gaveshalabs/weatherkids-hardware/Version 2.0/Core/Prelim Desing/Procuments details/HS Code confimation letter..pdf

Deputy Director of Customs

Customs Department Katunayake,

Sri Lanka

Dear Deputy Director,

I hope this letter finds you well. I am writing to approve the clearance process of my educational weather computer device under HS Code 9025.90, as you concluded after the inspection.

Thank you for your cooperation.

Sincerely,

Ushan Chaminda

Educator/ Engineer
