gaveshalabs/weatherkids-hardware/Version 2.0/Core/Prelim Desing/Procuments details/Invoice.pdf

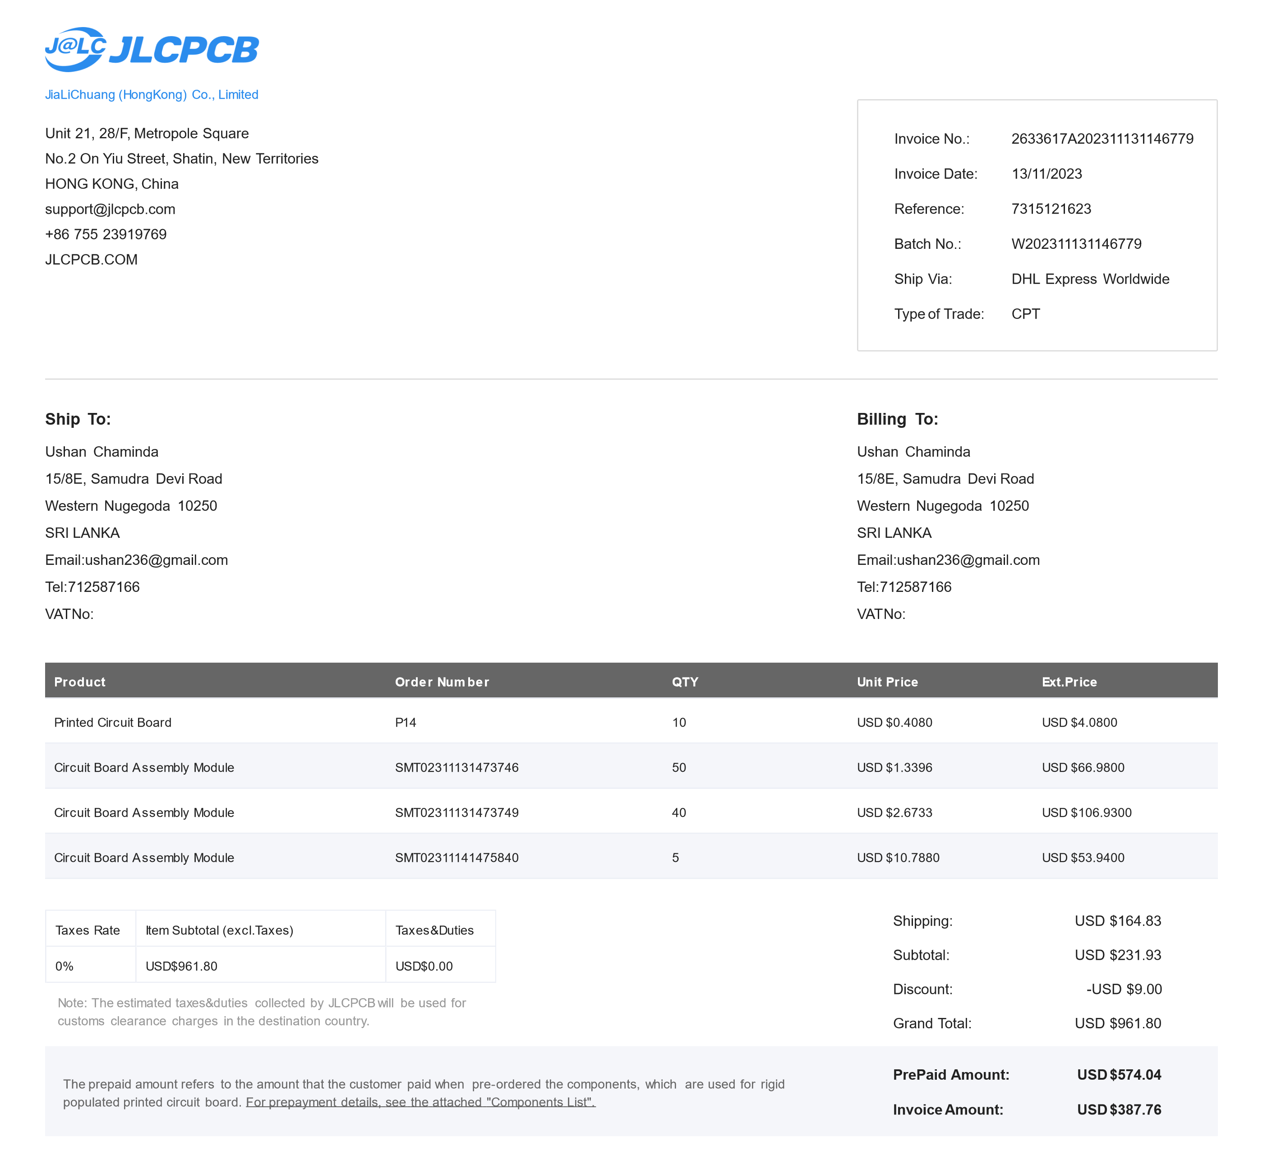
[picture p2: page 1]
