gaveshalabs/weatherkids-hardware/Version 2.0/Core/Weather Computer/_CAD Files/Stickers/Rain Scale - Laminated.pdf

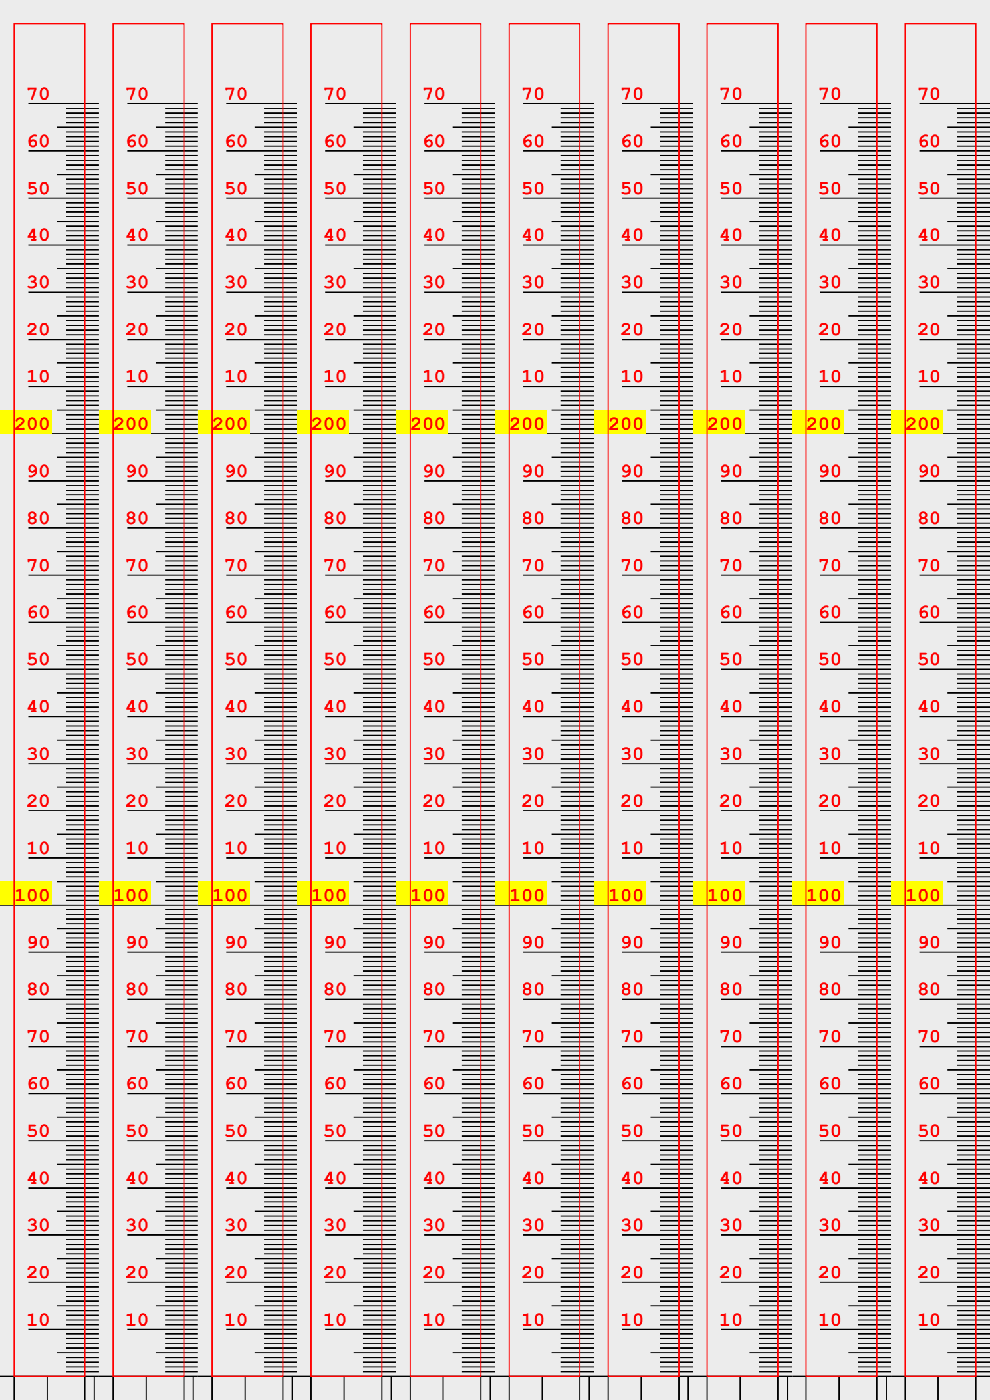
[picture p3: figure]
