gaveshalabs/weatherkids-hardware/Version 2.0/Core/Weather Computer/Resources/Connectors/DC-044D-2.5A-2.5-SMT.pdf

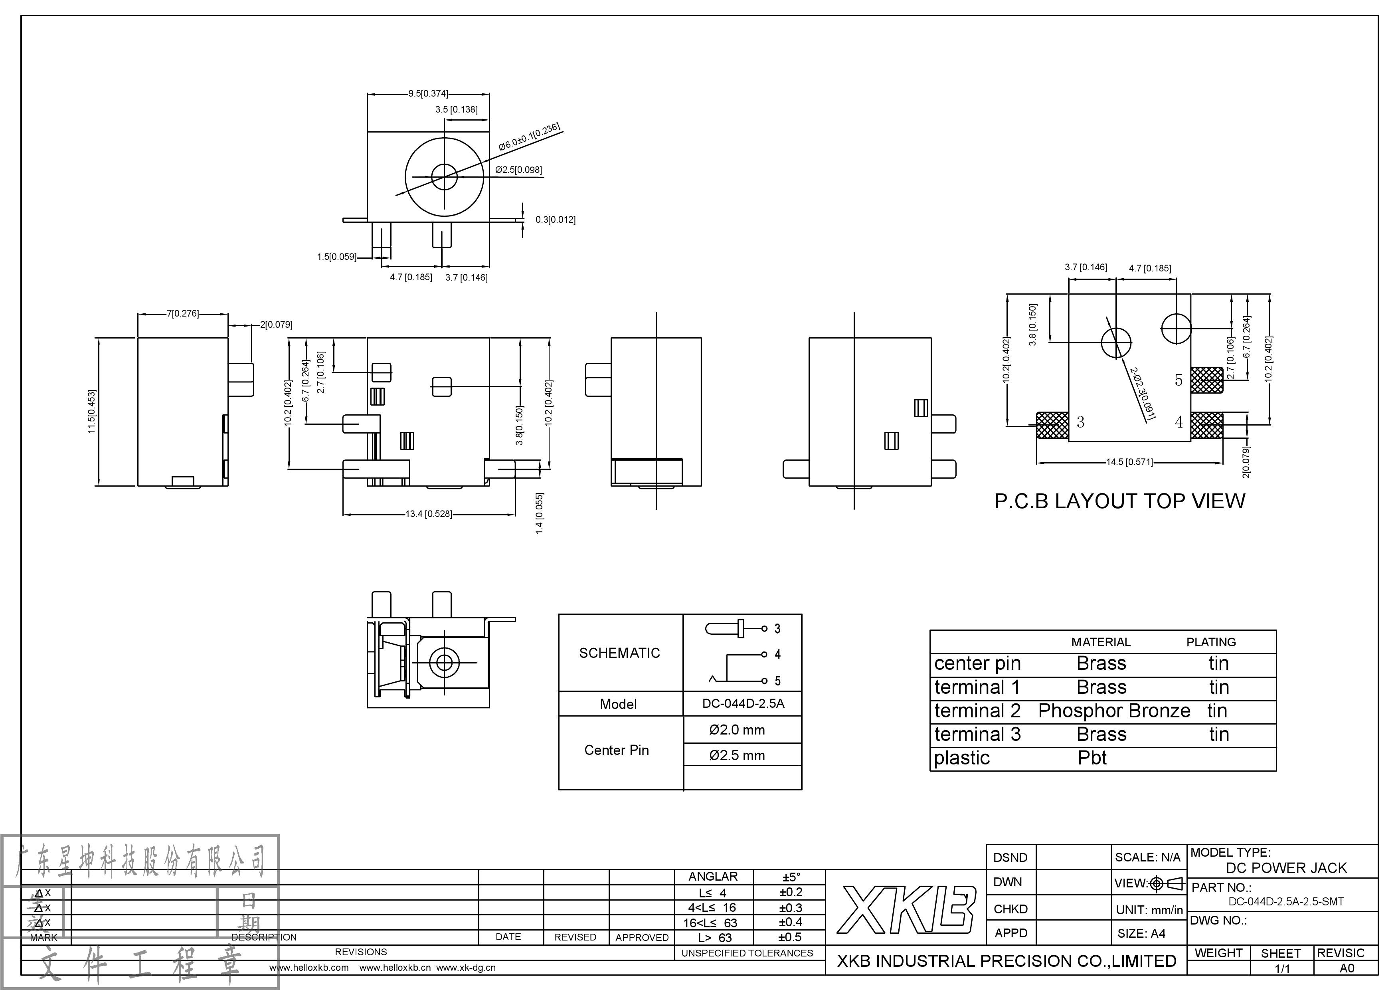
[picture p4: page 1]
