gaveshalabs/weatherkids-hardware/Version 2.0/Core/Weather Computer/Notes/Connectors.xlsx

part | price | link
RJ11 port | 0.16 | https://jlcpcb.com/partdetail/203237-R_RJ11R06PA800/C189750
