gaveshalabs/weatherkids-hardware/Version 2.0/Core/Weather Computer/Resources/3D Models/S2B-PH-SM4-TB(LF)(SN)--3DModel-STEP-56544.STEP

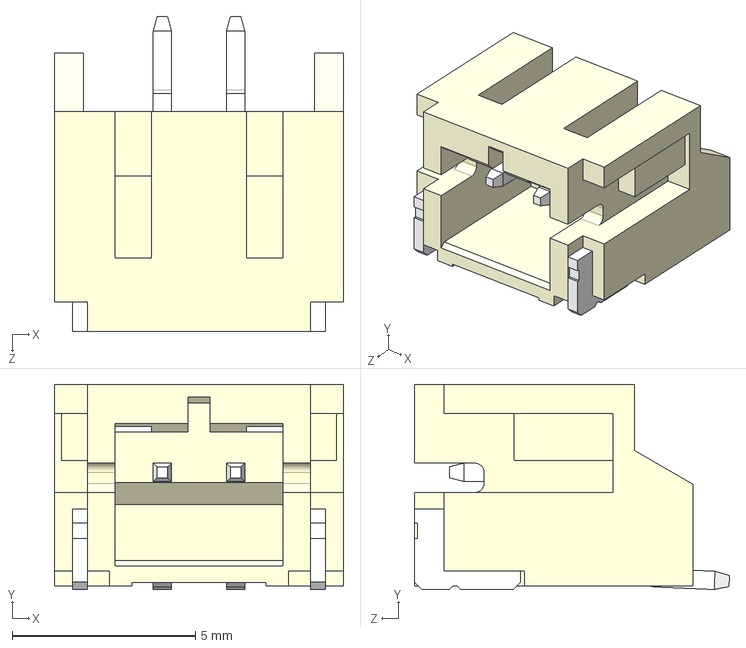
[picture p14: CAD file, 2024-11-12]
Version 2.0/Core/Weather Computer/Resources/3D Models/S2B-PH-SM4-TB(LF)(SN)--3DModel-STEP-56544.STEP
7.90 x 5.60 x 8.60 mm
