gaveshalabs/weatherkids-hardware/Version 2.0/Core/Weather Computer/Resources/USB C/usb-connector-type-c-female-1.snapshot.1/usb-type-c-smd-12pin-smd-1.snapshot.1/USB_type_C_smd_12ps.stp

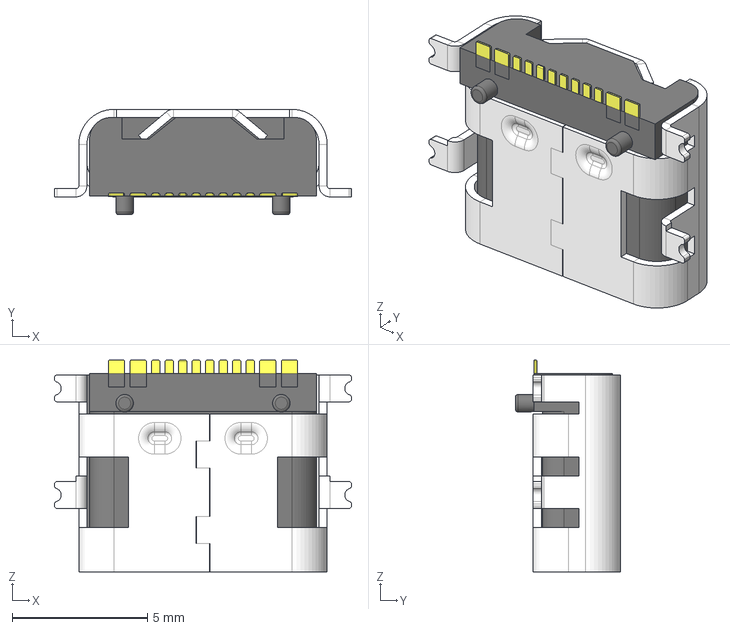
[picture p15: CAD file, 2024-11-12]
Version 2.0/Core/Weather Computer/Resources/USB C/usb-connector-type-c-female-1.snapshot.1/usb-type-c-smd-12pin-smd-1.snapshot.1/USB_type_C_smd_12ps.stp
11.0 x 3.90 x 7.85 mm
