gaveshalabs/weatherkids-hardware/Version 2.0/Solar Action Card/ENC/Production/SA_Bottom.STL

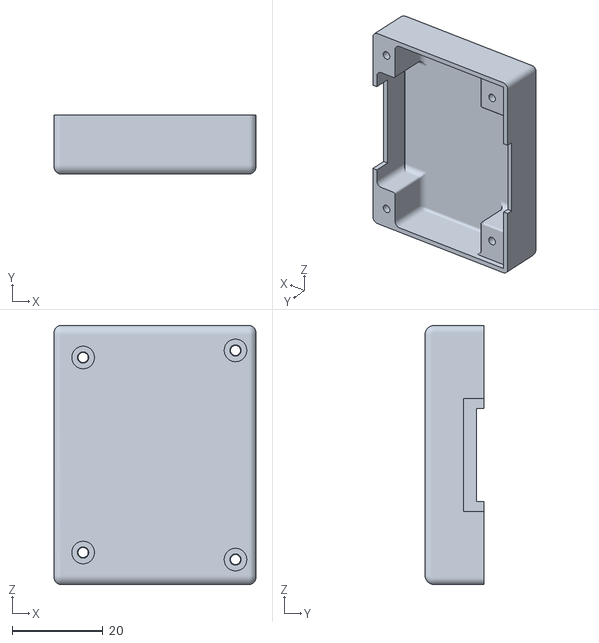
[picture p16: CAD file, 2024-11-12]
Version 2.0/Solar Action Card/ENC/Production/SA_Bottom.STL
44.5 x 13.0 x 57.1
