gaveshalabs/weatherkids-hardware/Version 2.0/Core/Weather Computer/_CAD Files/3D designs/OUTPUT/Clip mount.stl

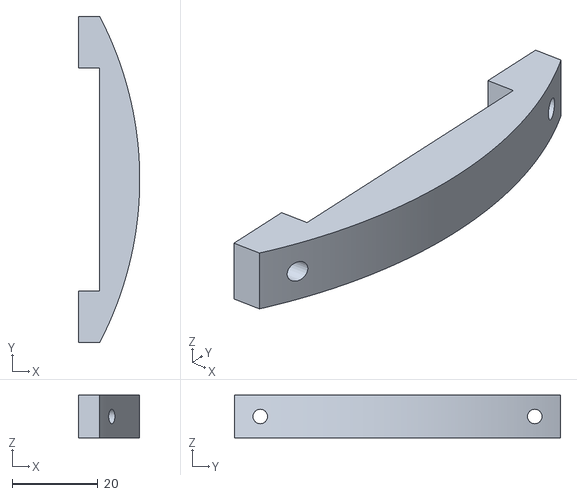
[picture p17: CAD file, 2024-11-12]
Version 2.0/Core/Weather Computer/_CAD Files/3D designs/OUTPUT/Clip mount.stl
14.3 x 76.0 x 10.00
