gaveshalabs/weatherkids-hardware/Version 2.0/Core/Weather Computer/_CAD Files/Parts/db125-35-8p-s.stp

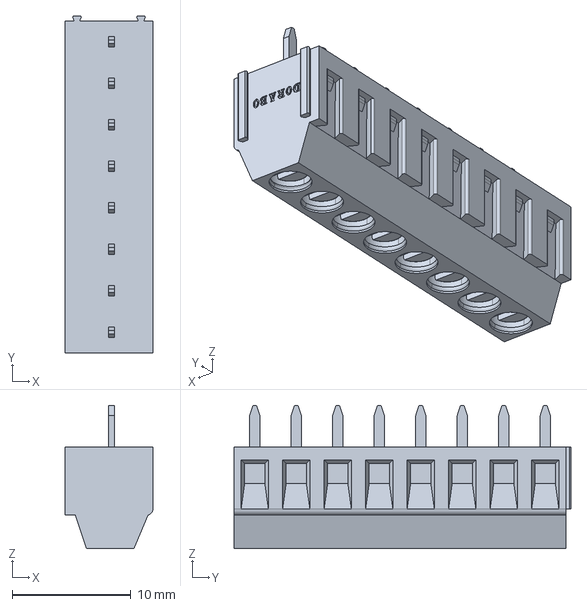
[picture p18: CAD file, 2024-11-12]
Version 2.0/Core/Weather Computer/_CAD Files/Parts/db125-35-8p-s.stp
7.40 x 28.4 x 12.1 mm
