gaveshalabs/weatherkids-hardware/Version 2.0/Solar Action Card/ENC/Production/SA_Top.STL

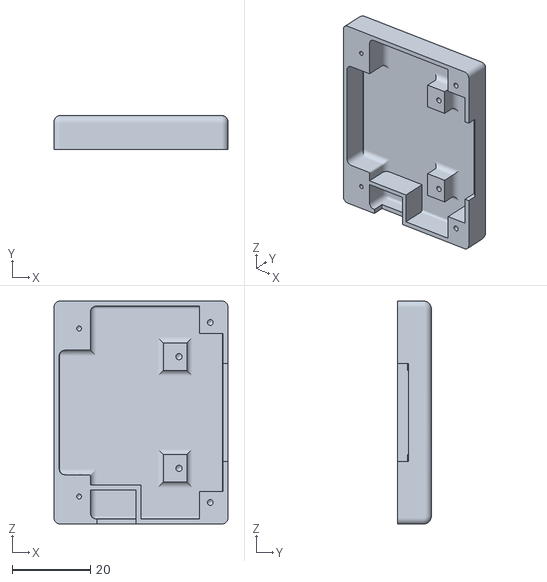
[picture p19: CAD file, 2024-11-12]
Version 2.0/Solar Action Card/ENC/Production/SA_Top.STL
44.5 x 8.65 x 57.1
