gaveshalabs/weatherkids-hardware/Version 2.0/Core/Weather Computer/_CAD Files/3D designs/OUTPUT/WS Pole Clip.stl

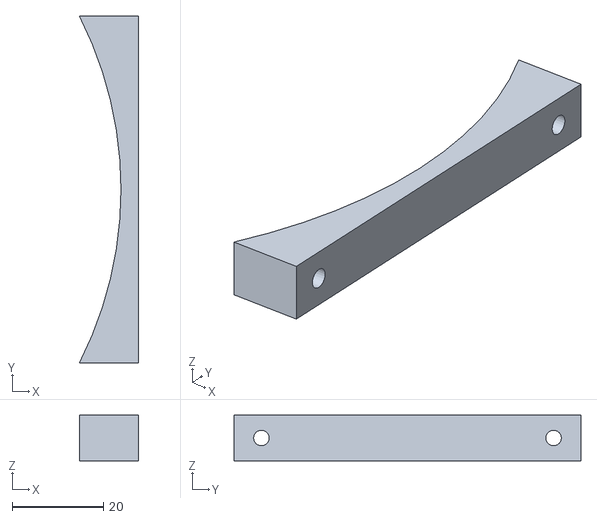
[picture p20: CAD file, 2024-11-12]
Version 2.0/Core/Weather Computer/_CAD Files/3D designs/OUTPUT/WS Pole Clip.stl
13.0 x 76.0 x 10.0
