gaveshalabs/weatherkids-hardware/Version 2.0/Core/Weather Computer/_CAD Files/Parts/db125-381-2p-s.stp

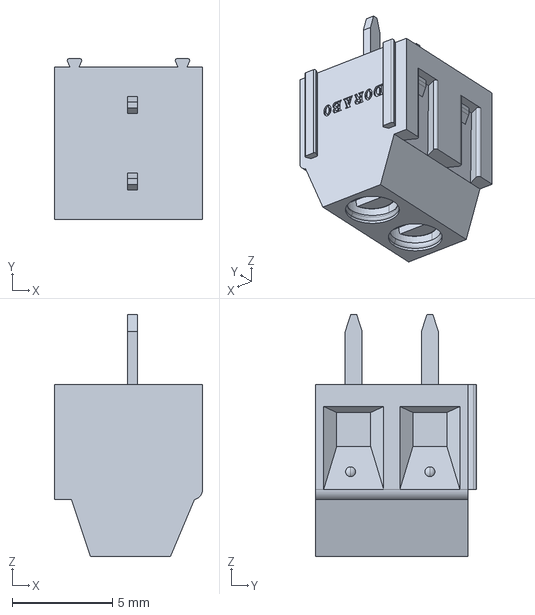
[picture p21: CAD file, 2024-11-12]
Version 2.0/Core/Weather Computer/_CAD Files/Parts/db125-381-2p-s.stp
7.40 x 8.04 x 12.1 mm
