gaveshalabs/weatherkids-hardware/Version 2.0/Core/Weather Computer/ENC/Production/WC_Button.STL

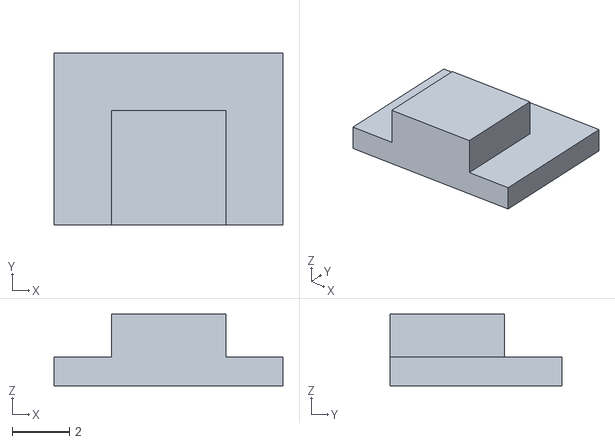
[picture p22: CAD file, 2024-11-12]
Version 2.0/Core/Weather Computer/ENC/Production/WC_Button.STL
8.00 x 6.00 x 2.50
