gaveshalabs/weatherkids-hardware/Version 2.0/Core/Weather Computer/ENC/WC_Button_Left.SLDPRT

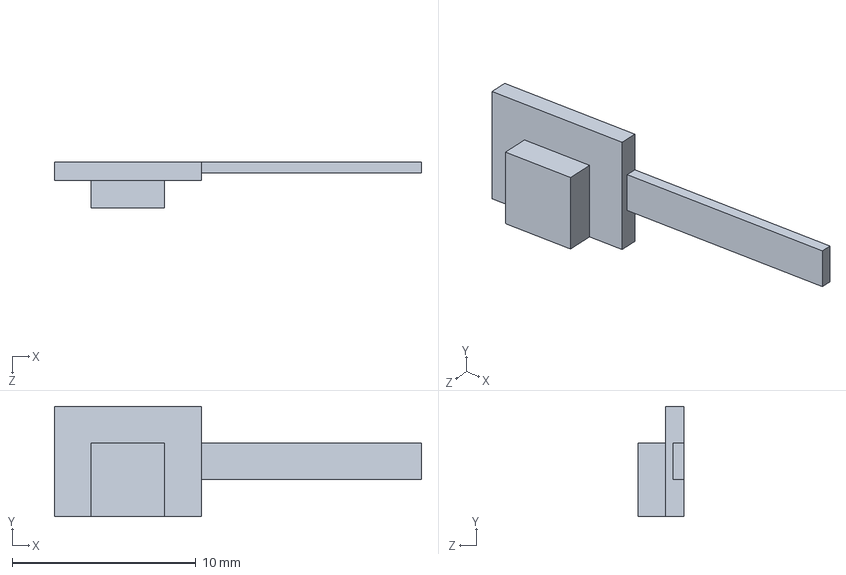
[picture p23: CAD file, 2024-11-12]
Version 2.0/Core/Weather Computer/ENC/WC_Button_Left.SLDPRT
20.0 x 6.00 x 2.50 mm
