gaveshalabs/weatherkids-hardware/Version 2.0/Core/Weather Computer/_CAD Files/3D designs/OUTPUT/Bucket Bracket.stl

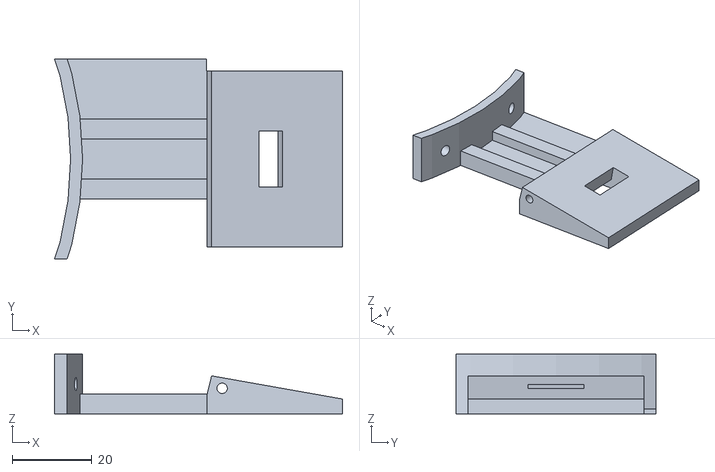
[picture p24: CAD file, 2024-11-12]
Version 2.0/Core/Weather Computer/_CAD Files/3D designs/OUTPUT/Bucket Bracket.stl
72.0 x 50.0 x 15.0
