gaveshalabs/weatherkids-hardware/Version 2.0/Core/Weather Computer/_CAD Files/3D designs/OUTPUT/WK Top.stl

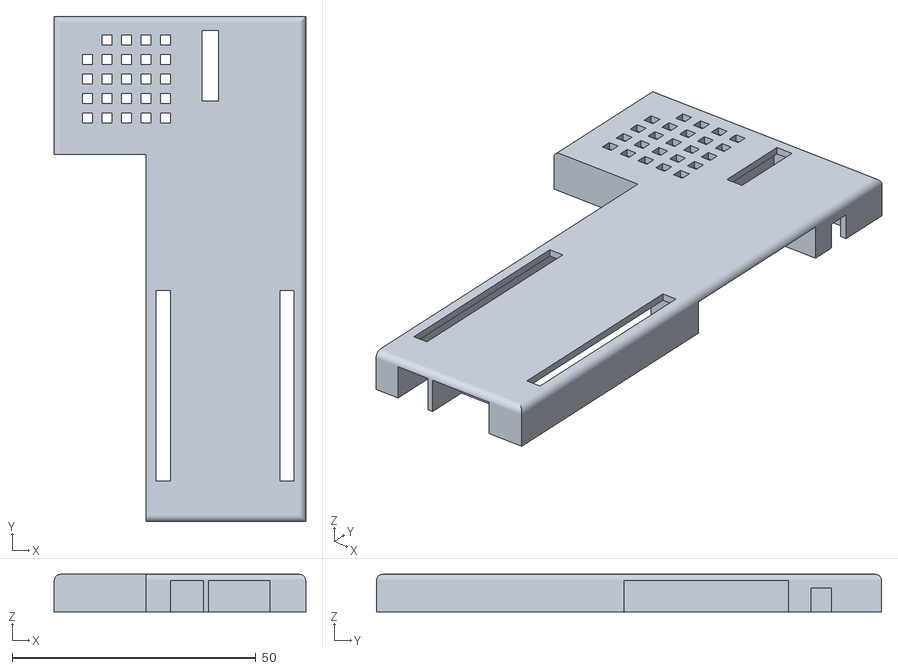
[picture p25: CAD file, 2024-11-12]
Version 2.0/Core/Weather Computer/_CAD Files/3D designs/OUTPUT/WK Top.stl
51.6 x 103.6 x 7.70
