gaveshalabs/weatherkids-hardware/Version 2.0/Core/Weather Computer/_CAD Files/3D designs/OUTPUT/WK Bottom.stl

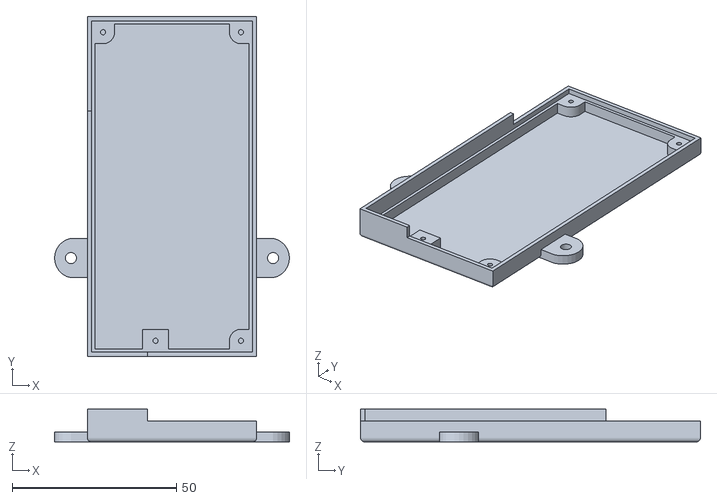
[picture p26: CAD file, 2024-11-12]
Version 2.0/Core/Weather Computer/_CAD Files/3D designs/OUTPUT/WK Bottom.stl
71.6 x 103.6 x 10.0
