gaveshalabs/weatherkids-hardware/Version 2.0/Core/Weather Computer/_CAD Files/3D designs/OUTPUT/WS mini Solar mounter.stl

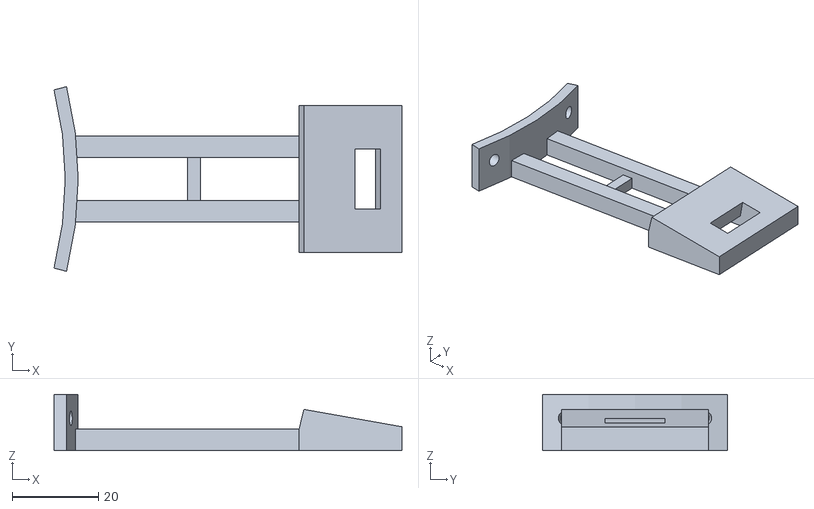
[picture p27: CAD file, 2024-11-12]
Version 2.0/Core/Weather Computer/_CAD Files/3D designs/OUTPUT/WS mini Solar mounter.stl
80.6 x 42.8 x 13.0
