gaveshalabs/weatherkids-hardware/Version 2.0/Core/Weather Computer/Resources/Connectors/MYOUNG-BH-18650-B1BA002_C2988620.pdf

环保

RoHs | K型

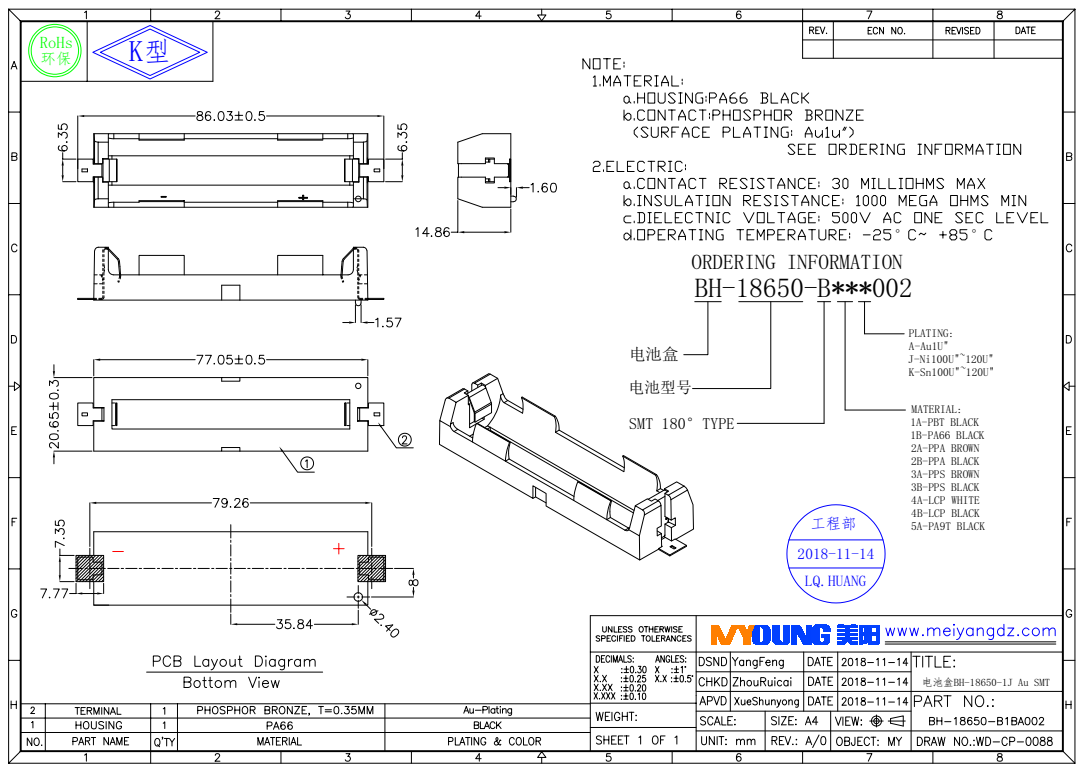
[picture p33: page 1]
工程部; LQ.HUANG; ORDERING INFORMATION; PLATING: A-Au1U" J-Ni100U"~120U" K-Sn100U"~120U"; SMT 180°TYPE; MATERIAL: 1A-PBT BLACK 1B-PA66 BLACK 2A-PPA BROWN 2B-PPA BLACK 3A-PPS BROWN 3B-PPS BLACK 4A-LCP WHITE 4B-LCP BLACK 5A-PA9T BLACK; 电池盒; 电池型号

电池盒BH-18650-1J Au SMT
