gaveshalabs/weatherkids-hardware/Version 2.0/Core/Weather Computer/Notes/R-RJ11R06P-A800.pdf

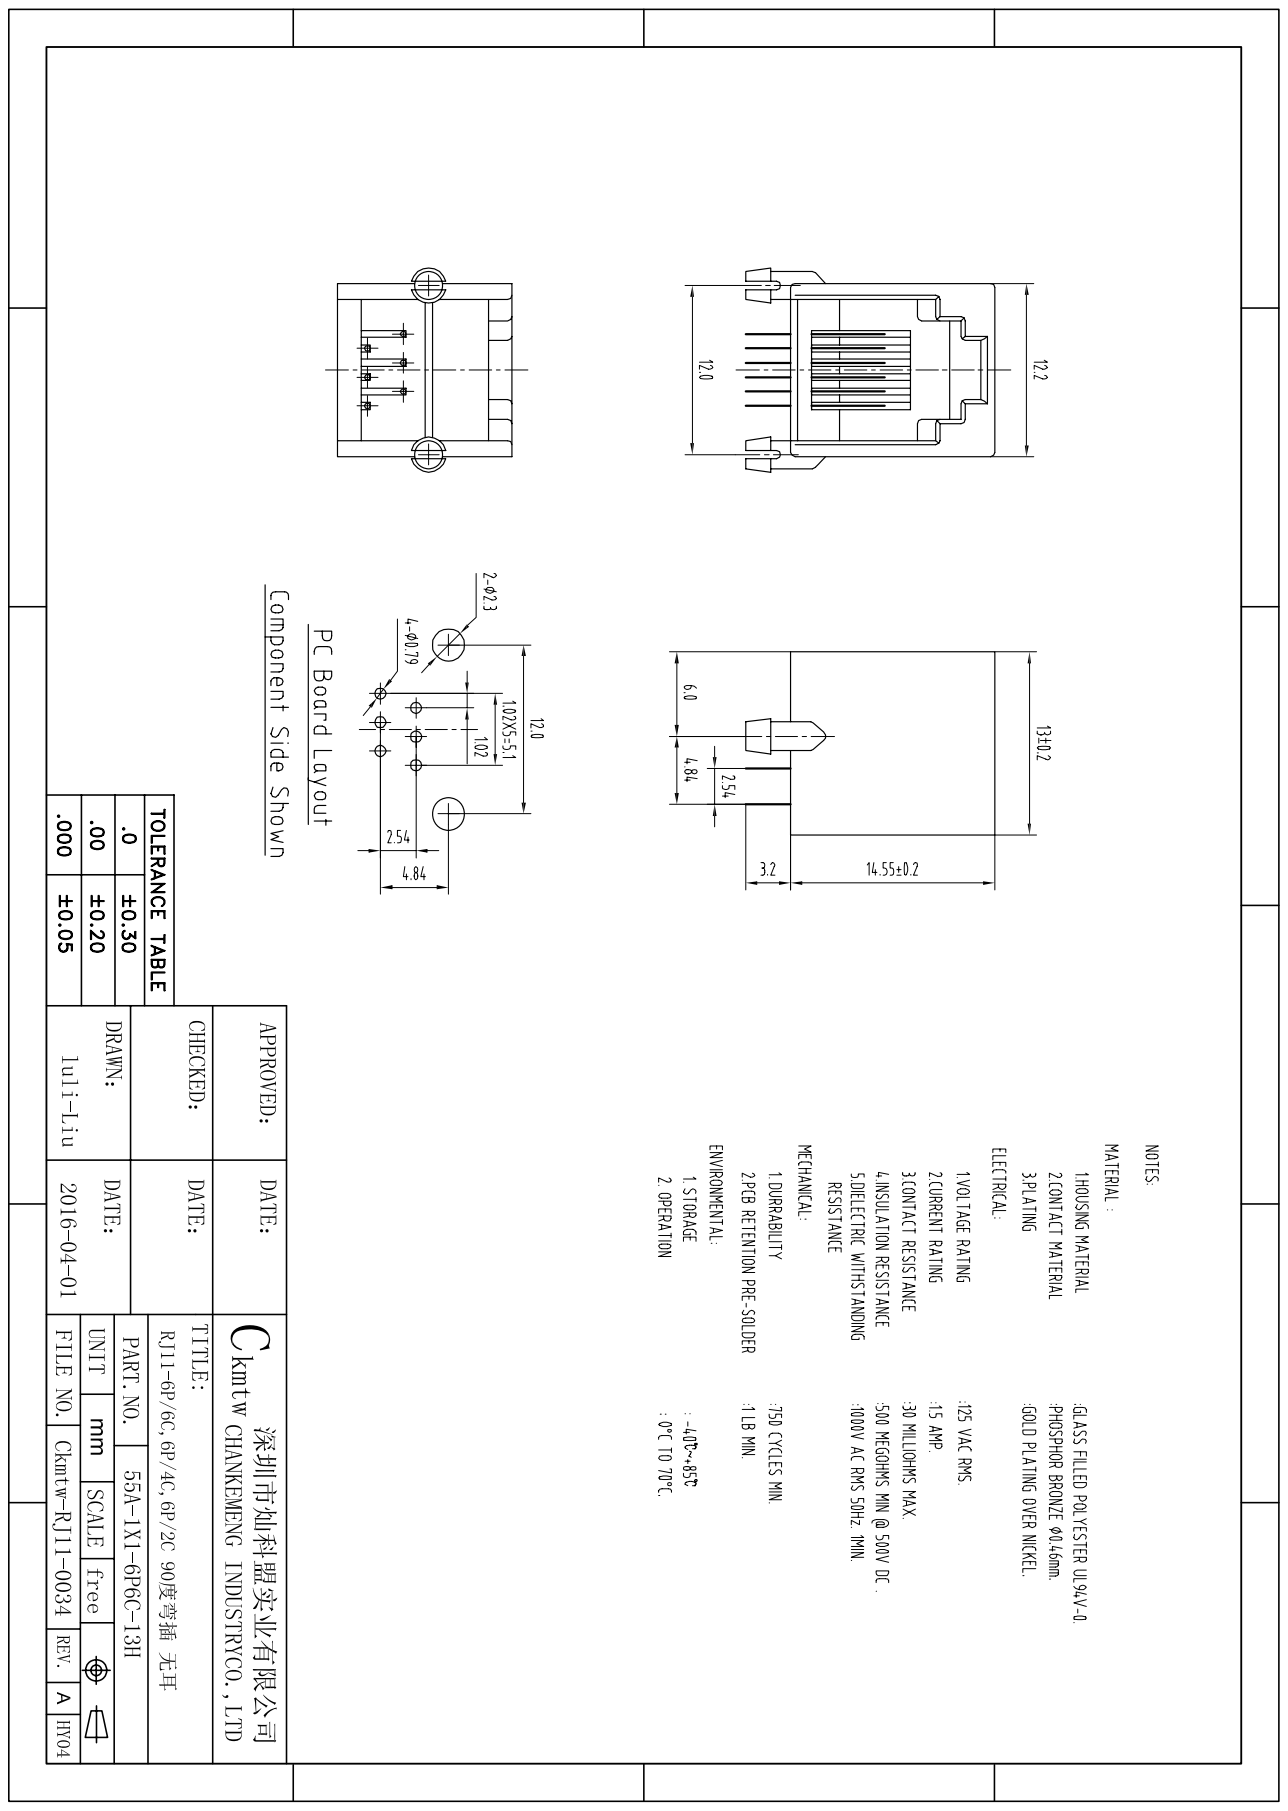
[picture p40: page 1]
