gaveshalabs/weatherkids-hardware/Version 2.0/Core/Weather Computer/_CAD Files/Stickers/Input Box Sticker.pdf

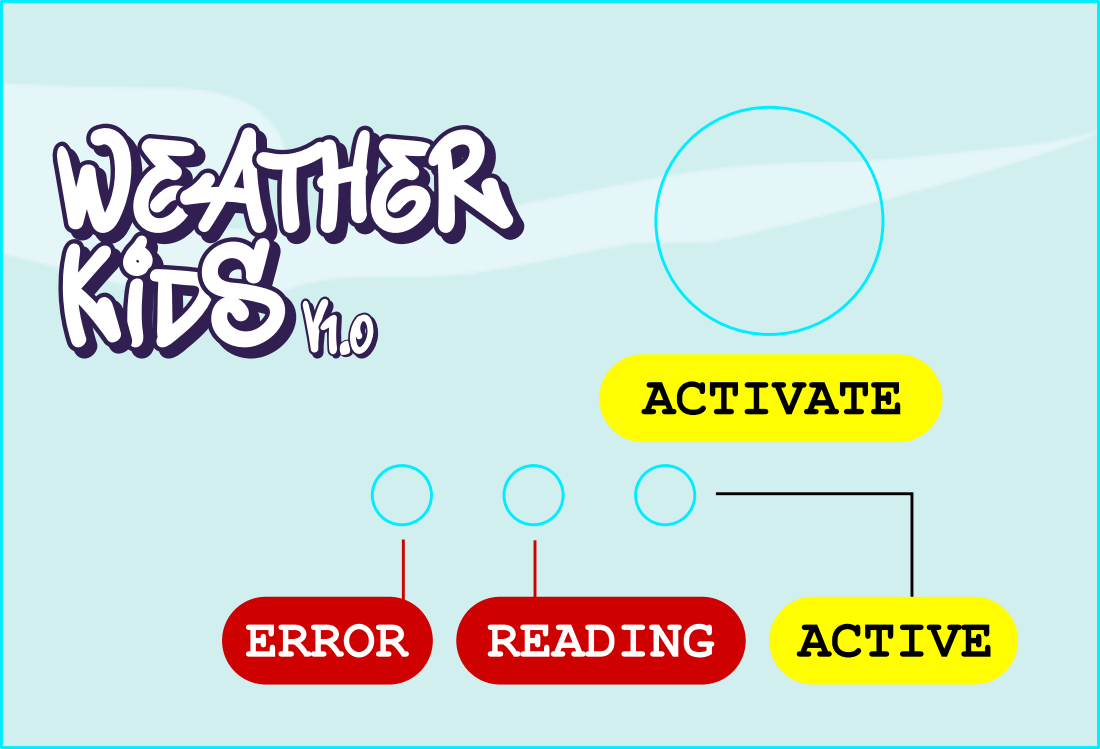
[picture p41: page 1]
READING; ACTIVATE; ERROR; ACTIVE
