gaveshalabs/weatherkids-hardware/Version 1.0/WeatherKids_Compact(V1.0)/_CAD Files/Stickers/SKU Sticker -  Laminated.pdf

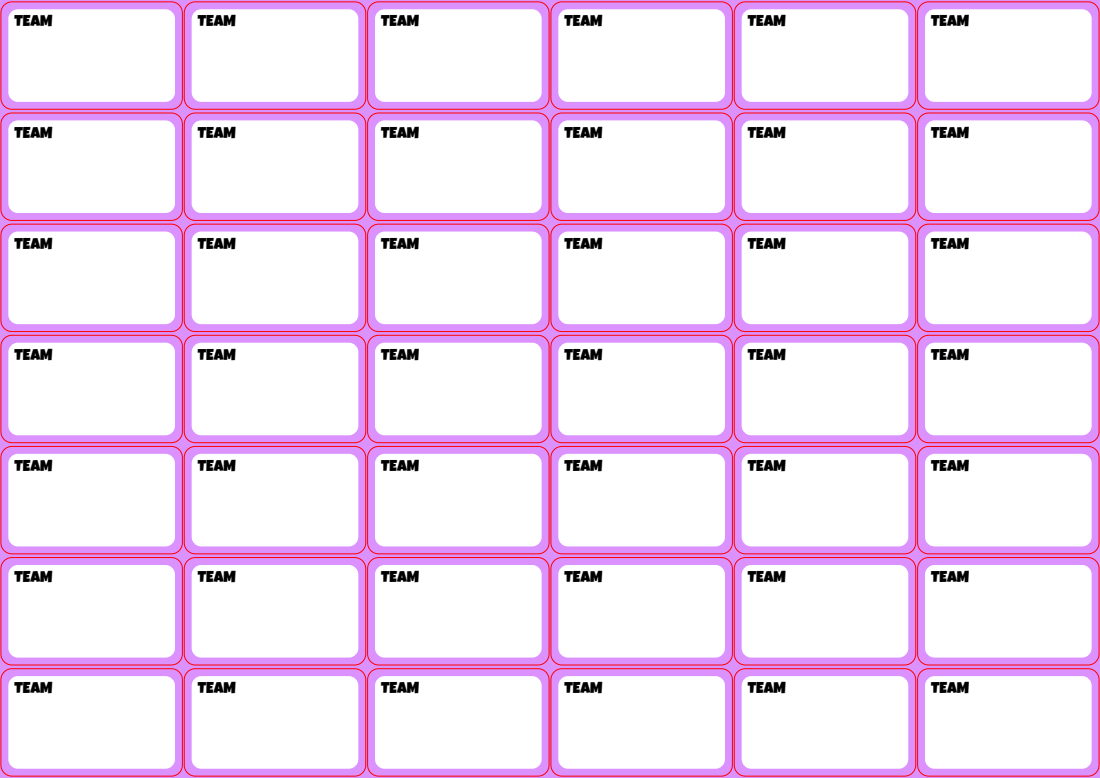
[picture p42: page 1]

TEAM | TEAM | TEAM | TEAM | TEAM | TEAM
