gaveshalabs/weatherkids-hardware/Version 2.0/Core/Weather Computer/_CAD Files/Stickers/Weather Station Notice board.pdf

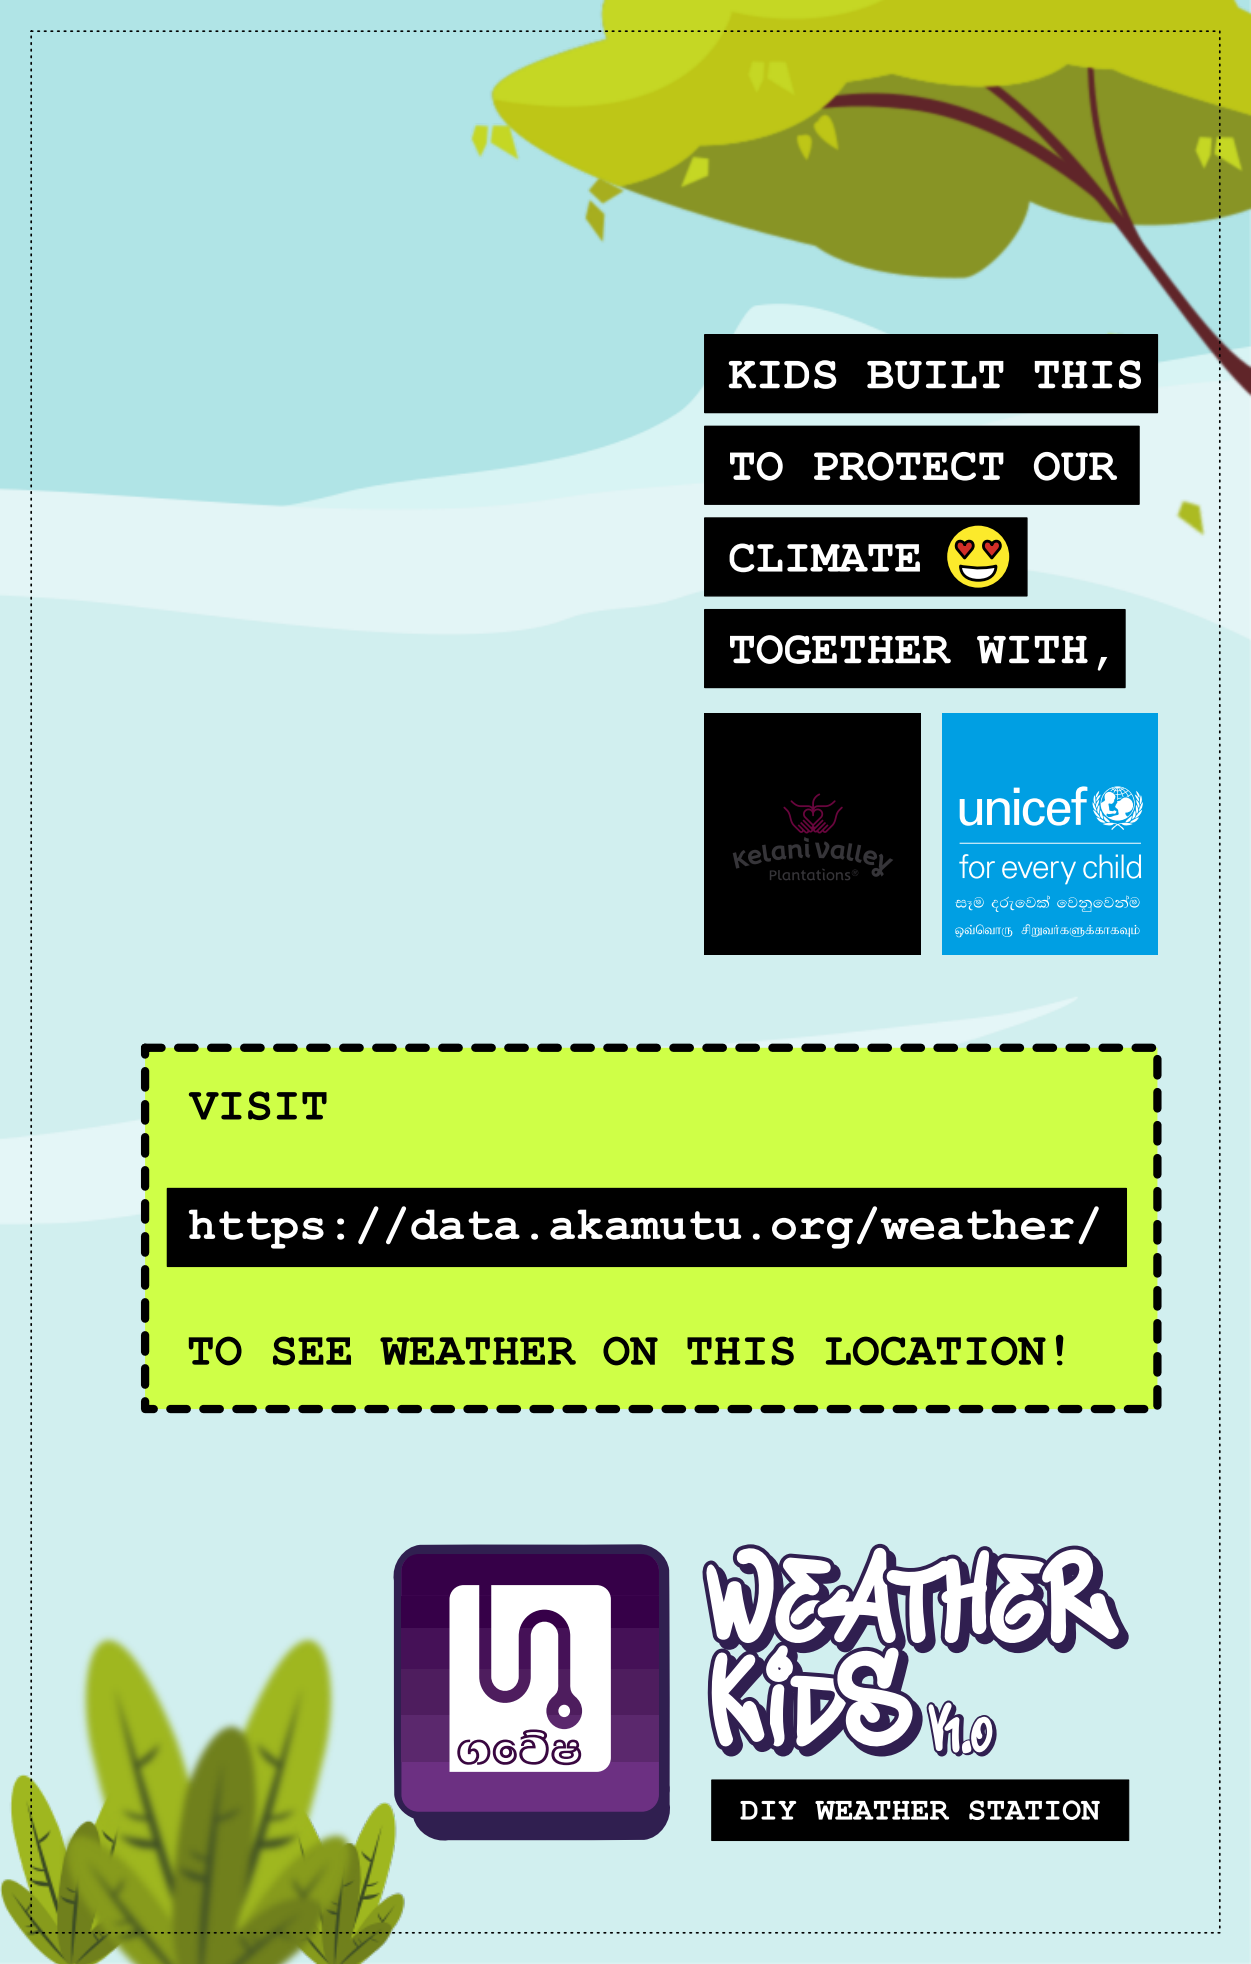
[picture p43: page 1]
