gaveshalabs/weatherkids-hardware/Version 2.0/Core/Weather Computer/Resources/Connectors/MY-18650-02.pdf

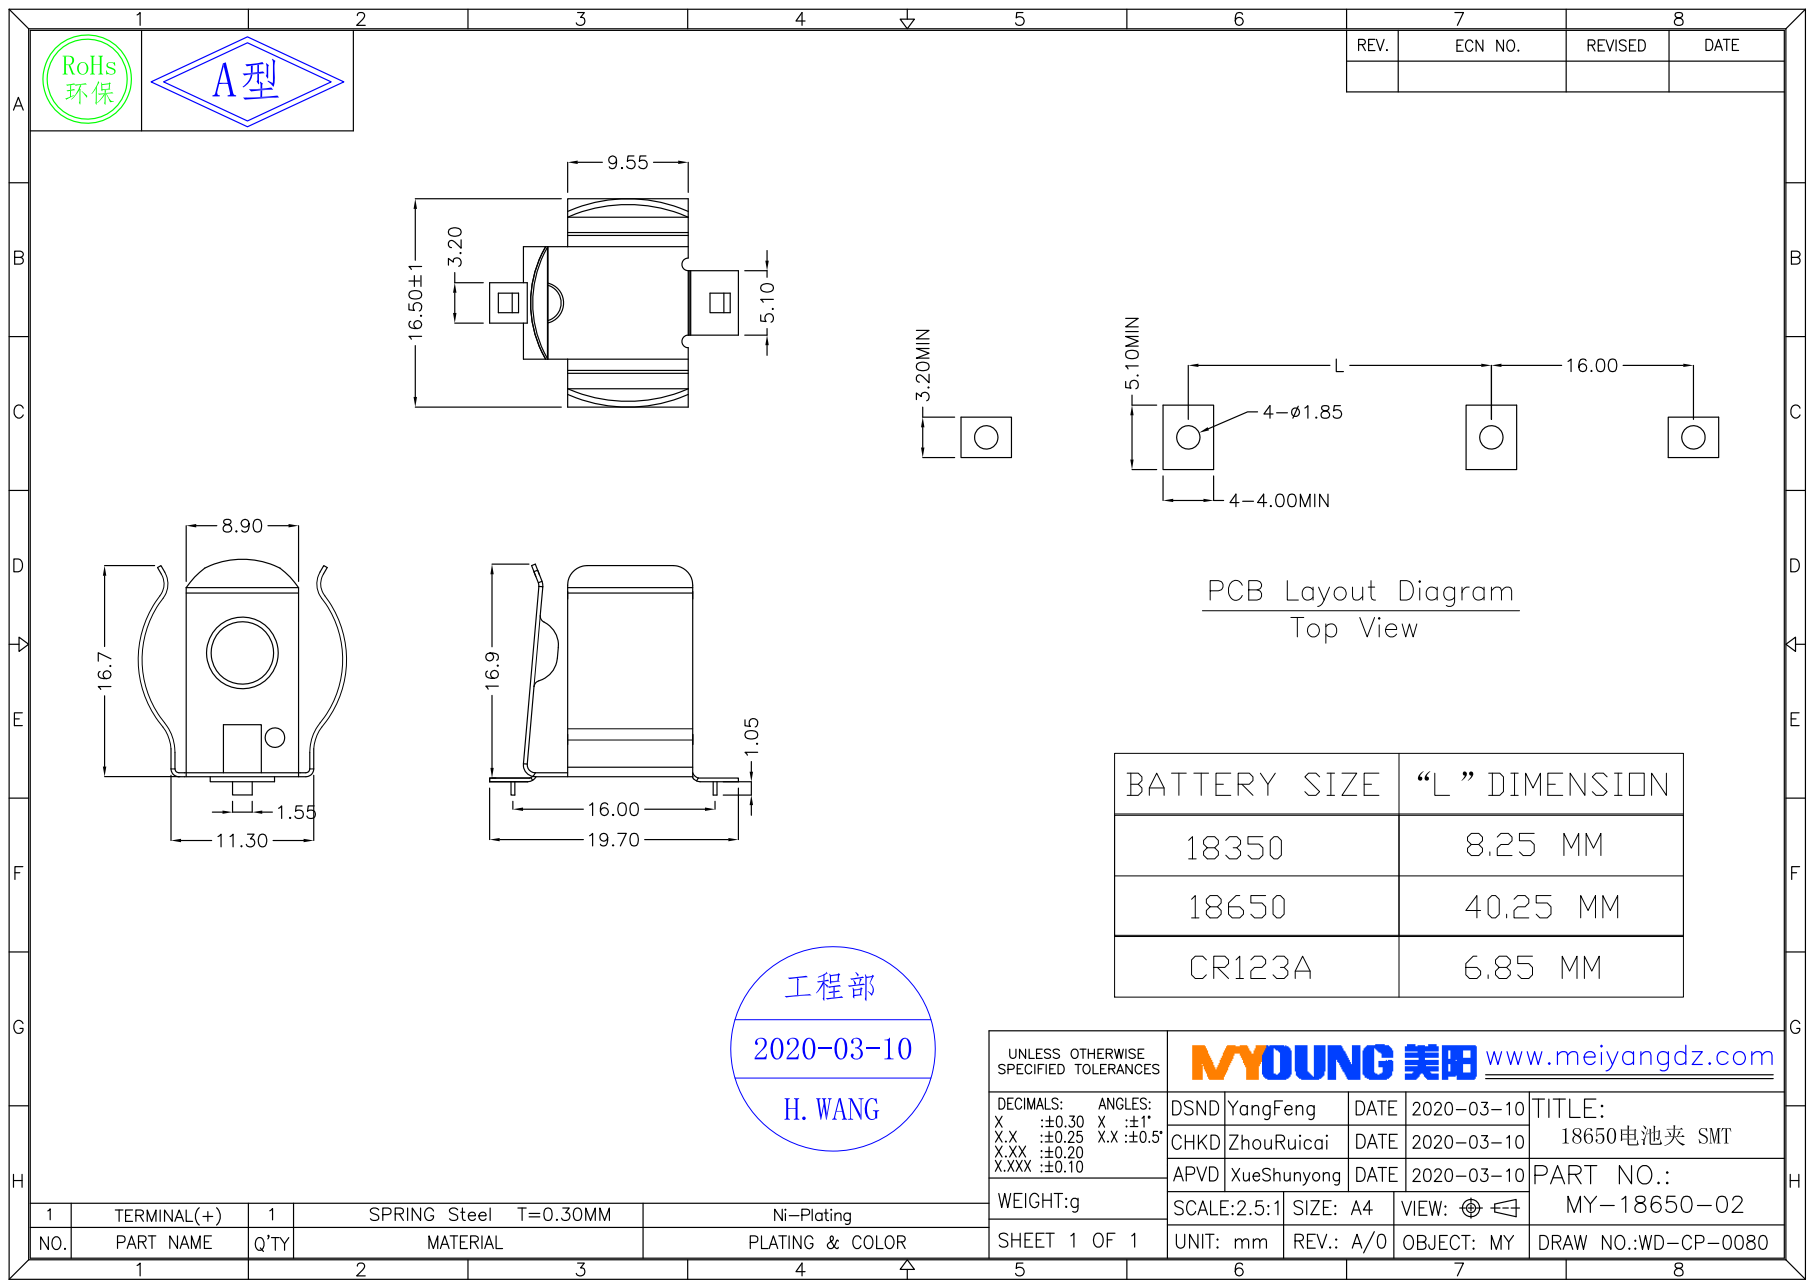
[picture p44: page 1]
