gaveshalabs/weatherkids-hardware/Version 2.0/Core/Weather Computer/Resources/Connectors/MYOUNG-MY-18650-01_C2979183.pdf

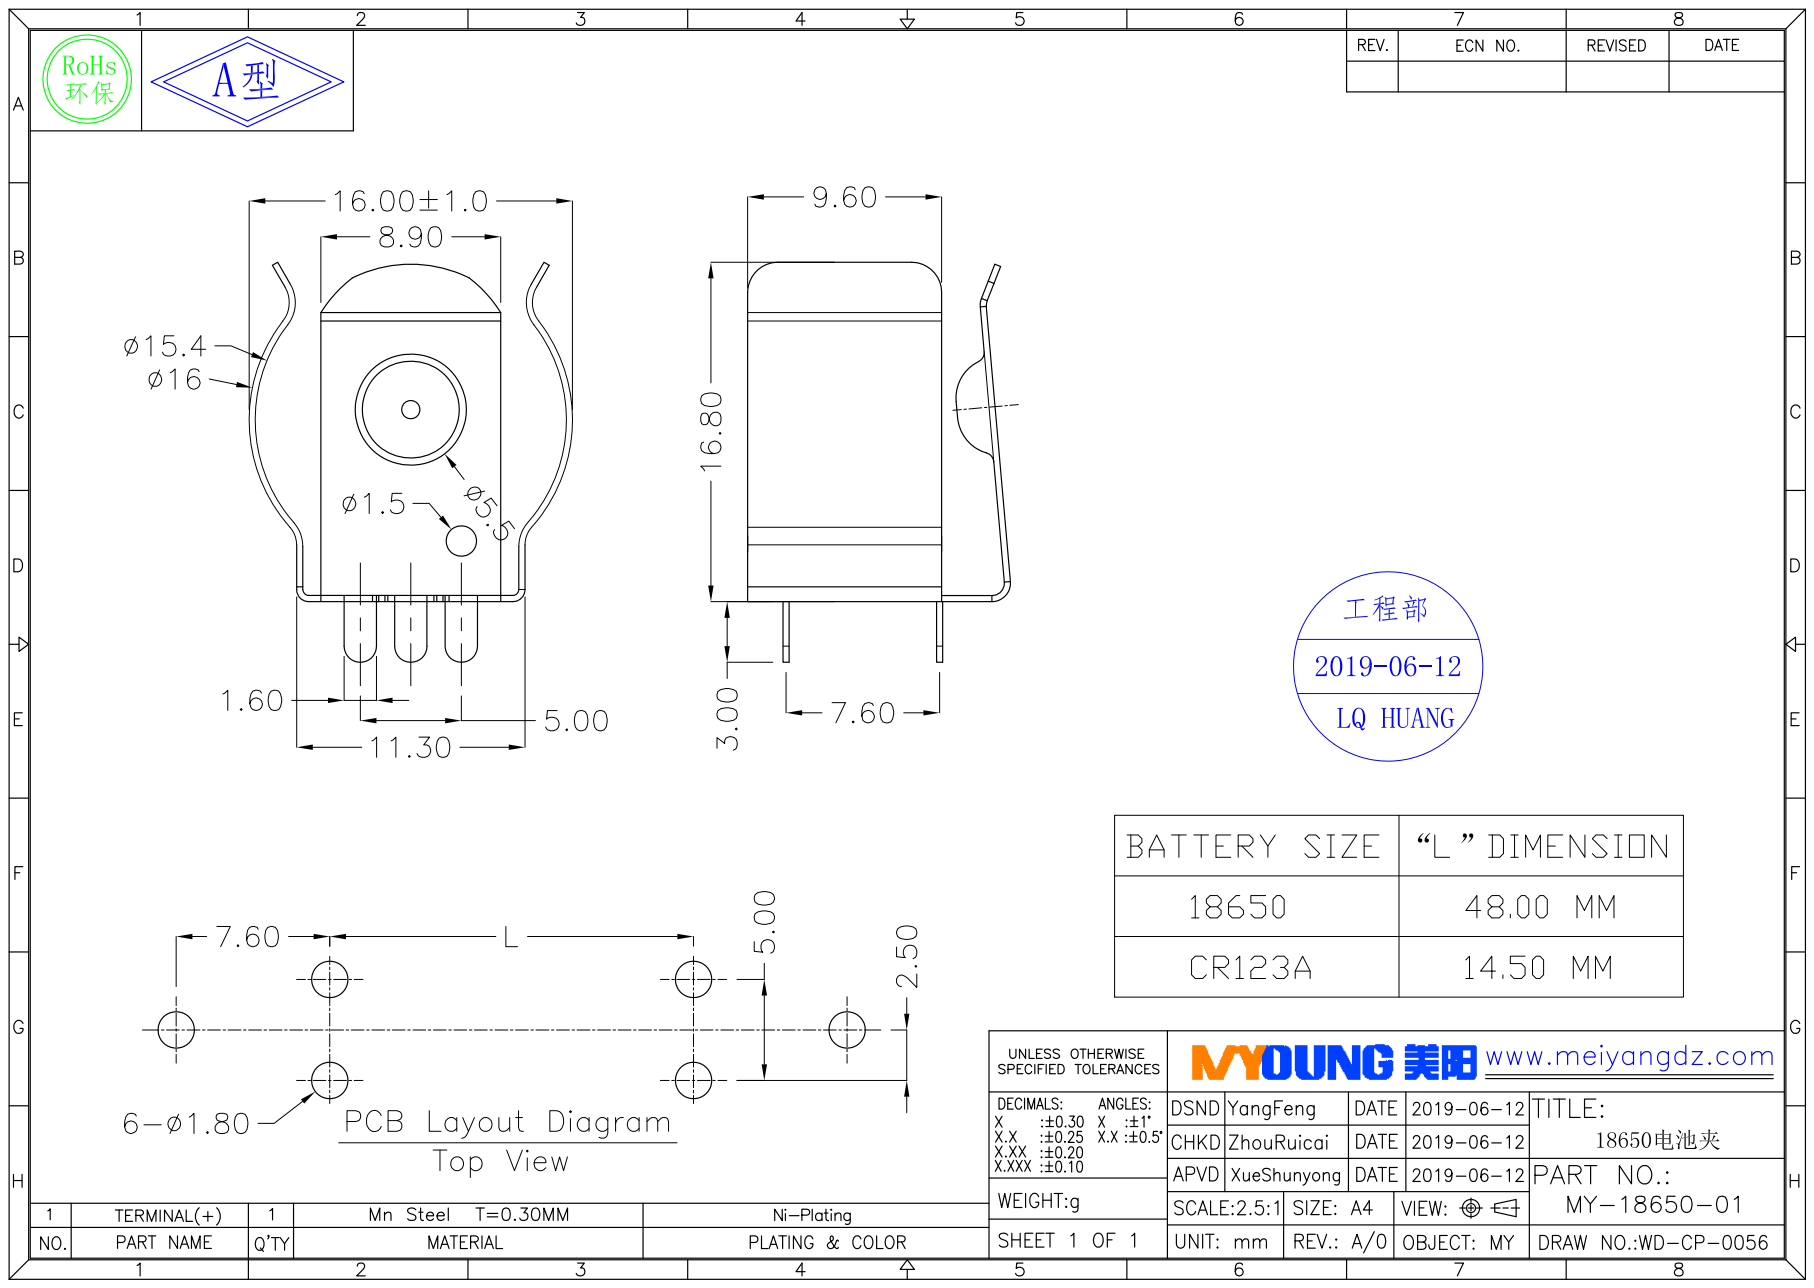
[picture p45: page 1]
