gaveshalabs/weatherkids-hardware/Version 2.0/Core/Weather Computer/Resources/Switch/XKB5858-X-E.pdf

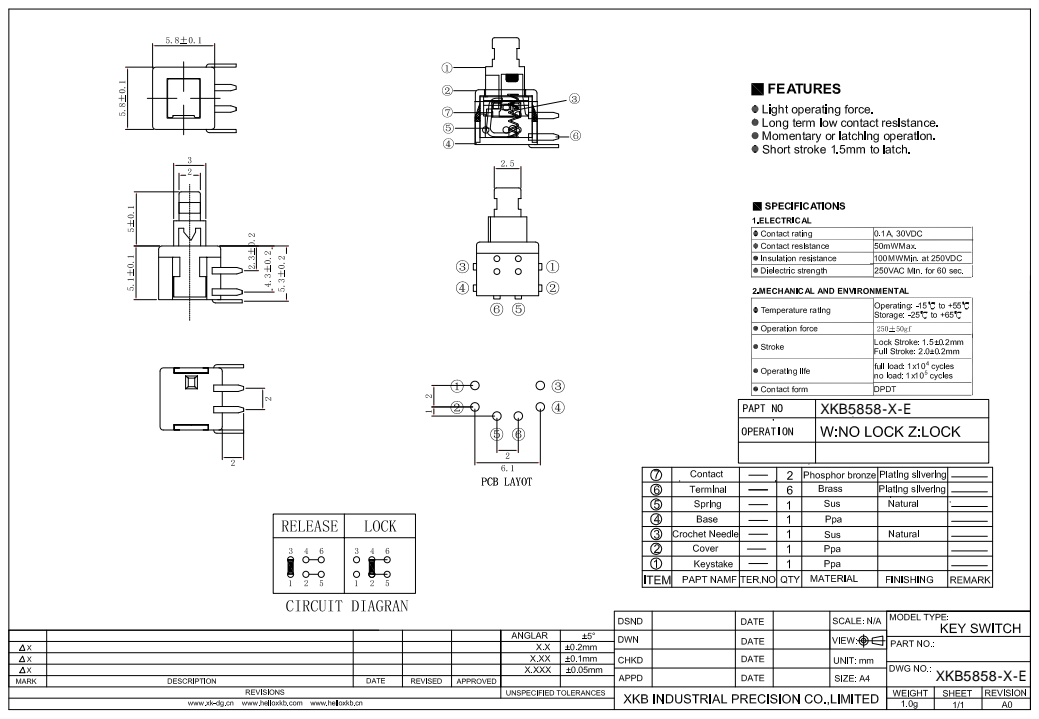
[picture p46: page 1]
XKB5858-X-E
